Dade3e/WolfHideAndSeek/infected_game/icons.h

const uint8_t PROGMEM infected_rabbit64[] = {
0x0, 0x0, 0x0, 0x0, 0x0, 0x0, 0x0, 0x0, 0x0, 0x0, 0x0, 0x0, 0x0, 0x0, 0x0, 0x0, 
0x0, 0x0, 0x0, 0x0, 0x0, 0x0, 0x0, 0x0, 0x0, 0x0, 0x0, 0x0, 0x0, 0x0, 0x0, 0x0, 
0x0, 0x0, 0x0, 0xe0, 0x7, 0x0, 0x0, 0x0, 0x0, 0x0, 0x3, 0x80, 0x1, 0xc0, 0x0, 0x0, 
0x0, 0x0, 0x6, 0x0, 0x0, 0x60, 0x0, 0x0, 0x0, 0x0, 0x1c, 0x0, 0x0, 0x38, 0x0, 0x0, 
0x0, 0x0, 0x38, 0x0, 0x0, 0x1c, 0x0, 0x0, 0x0, 0x0, 0x70, 0x0, 0x0, 0xe, 0x0, 0x0, 
0x0, 0x0, 0xe0, 0x0, 0x0, 0x7, 0x0, 0x0, 0x0, 0x1, 0xe0, 0x0, 0x0, 0x7, 0x80, 0x0, 
0x0, 0x1, 0xc0, 0x0, 0x0, 0x3, 0x80, 0x0, 0x0, 0x3, 0xc0, 0x0, 0x0, 0x3, 0xc0, 0x0, 
0x0, 0x3, 0xc0, 0x0, 0x0, 0x3, 0xc0, 0x0, 0x0, 0x3, 0x80, 0x0, 0x0, 0x1, 0xc0, 0x0, 
0x0, 0x7, 0x80, 0x0, 0x0, 0x1, 0xe0, 0x0, 0x0, 0x7, 0x80, 0xf, 0xf0, 0x1, 0xe0, 0x0, 
0x0, 0x7, 0x80, 0x7f, 0xfe, 0x1, 0xe0, 0x0, 0x0, 0x7, 0x81, 0xff, 0xff, 0x81, 0xe0, 0x0, 
0x0, 0x7, 0x83, 0xf0, 0xf, 0xc1, 0xe0, 0x0, 0x0, 0x7, 0xcf, 0x80, 0x1, 0xf3, 0xe0, 0x0, 
0x0, 0x3, 0xce, 0x0, 0x0, 0x73, 0xc0, 0x0, 0x0, 0x3, 0xfc, 0x0, 0x0, 0x3f, 0xc0, 0x0, 
0x0, 0x3, 0xf8, 0x0, 0x0, 0x1f, 0xc0, 0x0, 0x0, 0x1, 0xf0, 0x0, 0x0, 0xf, 0x80, 0x0, 
0x0, 0x1, 0xf8, 0x0, 0x0, 0x1f, 0x80, 0x0, 0x0, 0x7, 0xfc, 0xc, 0x30, 0x3f, 0xe0, 0x0, 
0x0, 0x1f, 0xff, 0x9e, 0x79, 0xff, 0xf8, 0x0, 0x0, 0x7f, 0xff, 0x12, 0x48, 0xff, 0xfe, 0x0, 
0x0, 0xff, 0xff, 0x12, 0x48, 0xff, 0xff, 0x0, 0x1, 0xff, 0xfe, 0x12, 0x48, 0x7f, 0xff, 0x80, 
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
B11111111, 
B11110011, 
B11110011, 
B11110011, 
B11110011, 
B11110011, 
B11110011, 
B11110011, 
B01111110, 
B11111111
};


//bullet 9X20
const uint8_t PROGMEM bullet8X20[]{
0x18, 0x3c, 0x3c, 0x7a, 0x7a, 0x7e, 0xff, 0xfd, 0xf9, 0xf9,
0xf9, 0xf9, 0xf9, 0xf9, 0xf9, 0xf9, 0xfd, 0xff, 0x7e, 0xff
};
