Dade3e/WolfHideAndSeek/infected_game/lora_part.ino

void sendMessage() {

  String myid = "";
  String for_who = "";
  if(myPlayerID < 10){
    myid = "0";
  }
  if(per_chi < 10){
    for_who = "0";
  }
  String outgoing = myid + String(myPlayerID) + for_who +  String(per_chi) + String(gameState);

  LoRa.beginPacket();
  LoRa.print(outgoing);                 // add payload
  LoRa.endPacket();                     // finish packet and send it
  
  Serial.print("message sent :");
  Serial.println(outgoing);
}

void lora_recv(){
  int packetSize = LoRa.parsePacket();
  
  if (packetSize) {
    Serial.println("");
    Serial.println("Received packet!");
    // read the packet
    message_recv = "";
    while (LoRa.available()) {
      message_recv += (char)LoRa.read();
    }
    int rssi = LoRa.packetRssi();
    // print the Packet and RSSI
    Serial.print("message_recv:\t");
    Serial.println(message_recv);
    Serial.print("rssi:\t\t");
    Serial.println(rssi);
    int da_chi = (message_recv[0] - '0')*10+(message_recv[1] - '0');
    int for_who = (message_recv[2] - '0')*10+(message_recv[3] - '0');
    int suo_valore = message_recv[4] - '0';

    senders[da_chi] = suo_valore;
    senders_rssi[da_chi] = rssi;
    check_message(da_chi, for_who, suo_valore, rssi);
    
    lastRecvTime = millis();
  }
}

void check_message(int da_chi, int for_who, int suo_valore, int rssi){
  //se sono Sano, controllo se qualcuno se sono vicino ad un infetto (gameState 1):
  if(gameState == 1){
    if(rssi >= sogliaRSSI && suo_valore == 3){
      //sono vicino ad un infetto, sono stato infettato
      if(displayOnOff == 1)
        schermata_infettato();
      lastCleanTime = millis() + 3000; //attesa per mostrare la schermata per 3 sec
      per_chi = da_chi;      
      gameState = 2;
      digitalWrite(speakerPin, HIGH);
    }
    else if(for_who == myPlayerID && suo_valore == 4){
      //ho la conferma di aver colpito un infetto
      schermata_HIT();
      per_chi = da_chi;
      sendMessage();
      lastCleanTime = millis();
    }
  }

  //sono in stato appena infettato, ho inviato, aspetto risposta
  else if(gameState == 2){
    if(for_who == myPlayerID){
      gameState = 3;
      per_chi = da_chi;
      lastSendTime = millis()-6000;
    }
  }

  //sono infetto
  else if(gameState == 3){
    //controllo se ho infettato
    if(suo_valore == 2 && for_who == myPlayerID){
      if(displayOnOff == 1)
        schermata_recv_infected();
      per_chi = da_chi;
      sendMessage();
      lastCleanTime = millis();
      memset(senders, 0, sizeof(senders));
    }
  }

  //invio morte
  else if(gameState == 4){
    //controllo se ho infettato
     if(for_who == myPlayerID){
      gameState = 5;
      per_chi = da_chi;
      lastSendTime = millis()-6000;
    }
  }
}
