Dade3e/WolfHideAndSeek/multi_games/ir_part.ino

//PARTE WERERABBIT
void shoot_wererabbit() {
  irsend.sendSony(440000+(myPlayerID*100)+id_wolf, 20, 2);  // 20 bits & 2 repeats
}

void receiveIR_wererabbit() {
  if (irrecv.decode(&results)) {
      int ir_value = results.value;
      Serial.println(ir_value);
      //head 101000
      if(ir_value/10000 == 44){
        id_wolf = (ir_value%440000)/100;
        int id_last_wolf = (ir_value%(440000 + id_wolf*100));
        controllo_colpito_wererabbit(id_last_wolf);
      }
      Serial.println(id_wolf);
      irrecv.resume(); // Receive the next value
  }
}

void controllo_colpito_wererabbit(int id_last_wolf){
  if(id_last_wolf == 0){
    if(id_wolf== myPlayerID){
      stato = 0;
    }
  }
  else if(id_last_wolf == myPlayerID){
    lastSendTime = millis()-9000;
    myValue = 2; //invio segnale che ero ex wererabbit
    stato = 4; //stato ex wererabbit
  }
  else{
    lastSendTime = millis()-9000;
    myValue = 3;
    stato = 5; //Stato colpito
  }  
}

//PARTE INFECTED
void shoot_infected() {
  irsend.sendSony(440000+(myPlayerID*100), 20, 2);  // 20 bits & 2 repeats
}

void receiveIR_infected() {
  if (irrecv.decode(&results)) {
      int ir_value = results.value;
      Serial.println(ir_value);
      //head 101000
      if(ir_value/10000 == 44){
        id_wolf = (ir_value%440000)/100;
        lastSendTime = millis()-9000;
        myValue = 3;
        stato = 5; //Stato colpito
      }
      Serial.println(id_wolf);
      irrecv.resume(); // Receive the next value
  }
}

void controllo_colpito_infected(){
  
}
